fairwaves/umtrx-schematics/umsel-v1/pictures/UmSELv1-TOP-900.png

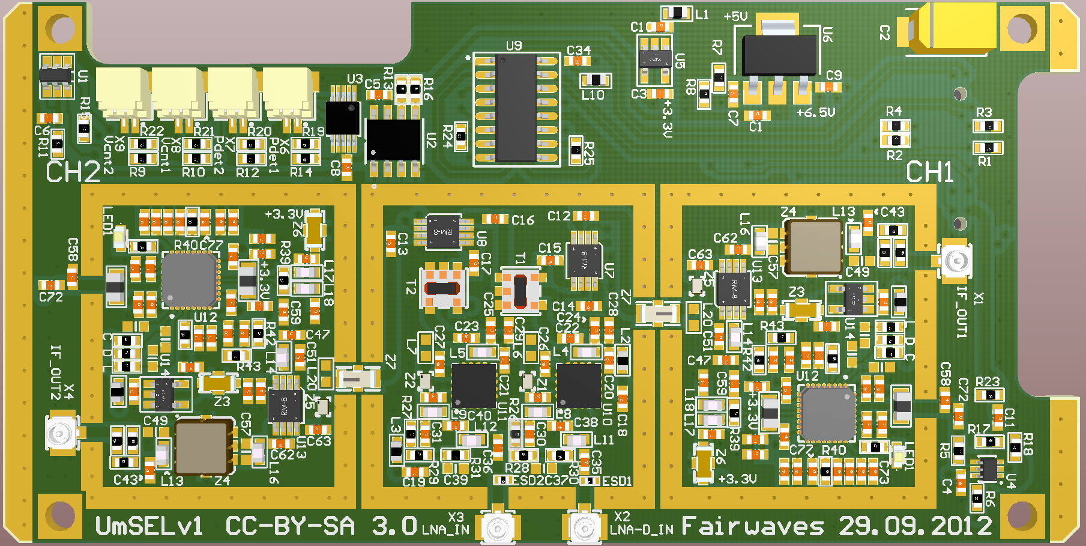
umsel-v1/pictures/UmSELv1-TOP-900.png
